AndreaFavero71/timelapse/pictures/IMG_20230702_124846.jpg

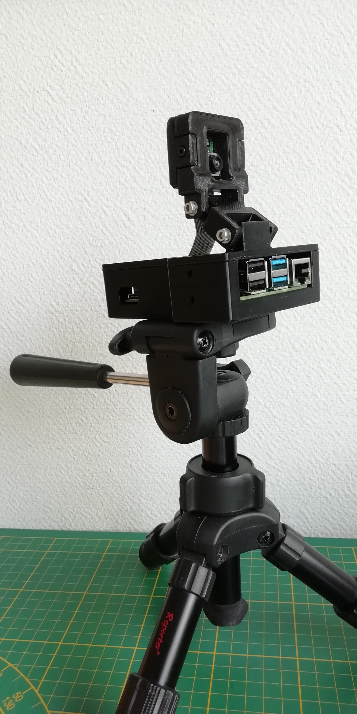
pictures/IMG_20230702_124846.jpg
