AndreaFavero71/timelapse/pictures/IMG_20230702_125228.jpg

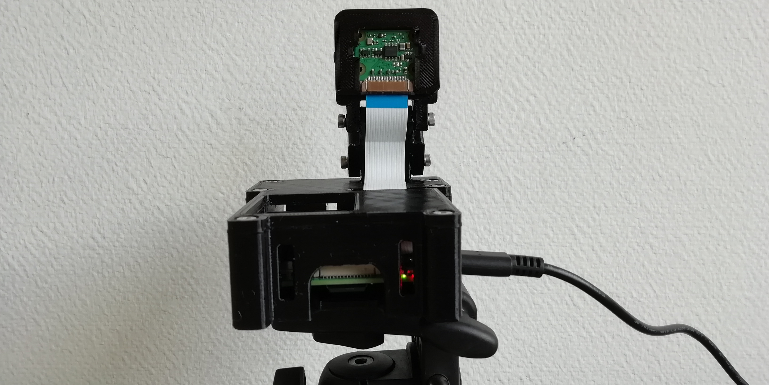
pictures/IMG_20230702_125228.jpg
